howie-j/opensolder/mechanical/images/side_1.png

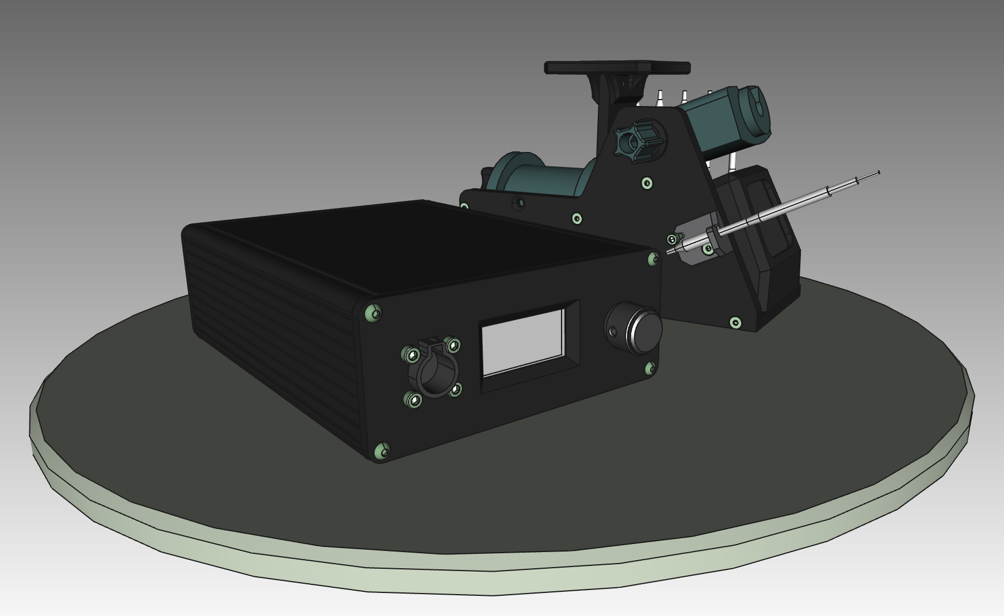
mechanical/images/side_1.png
