howie-j/opensolder/mechanical/images/top_3_ortho.png

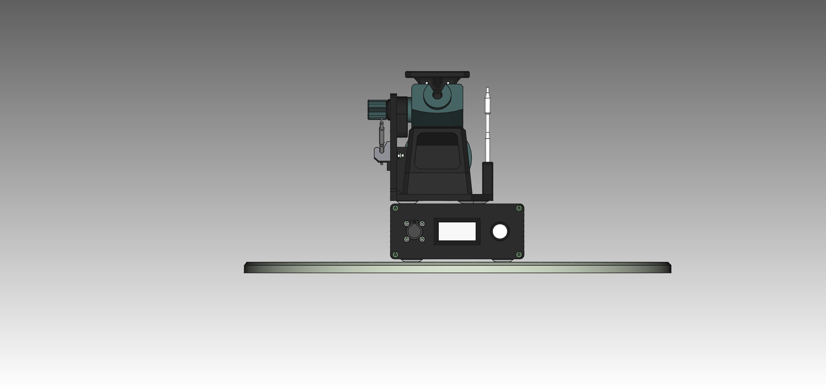
mechanical/images/top_3_ortho.png
