howie-j/opensolder/mechanical/step/stand_step_files/tool_holder_adapter.step

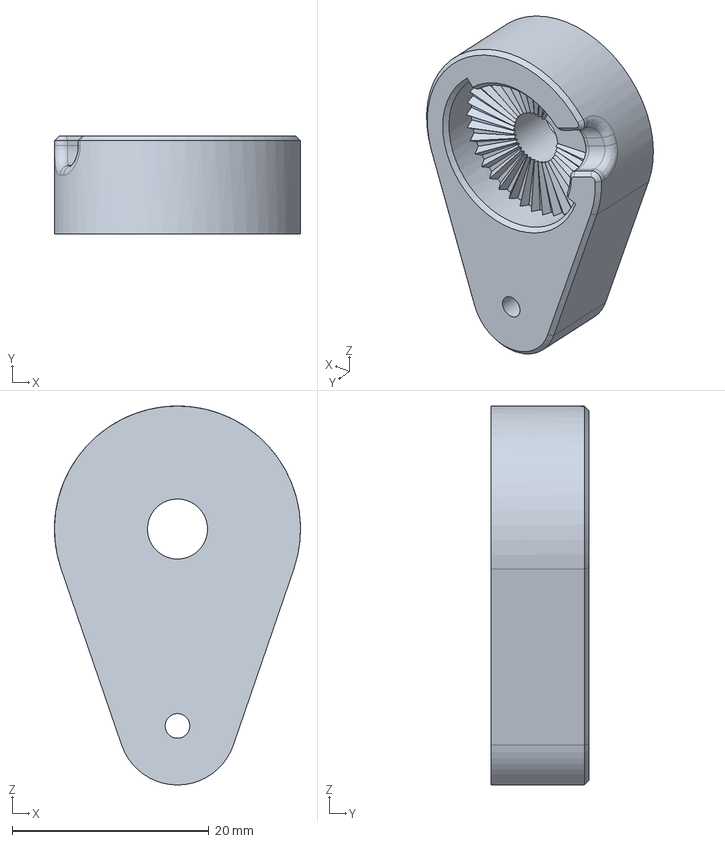
[picture p28: CAD file, 2023-04-08]
mechanical/step/stand_step_files/tool_holder_adapter.step
25.0 x 10.0 x 38.5 mm
