howie-j/opensolder/mechanical/freecad/Parts/Rotary Encoder Knob.FCStd

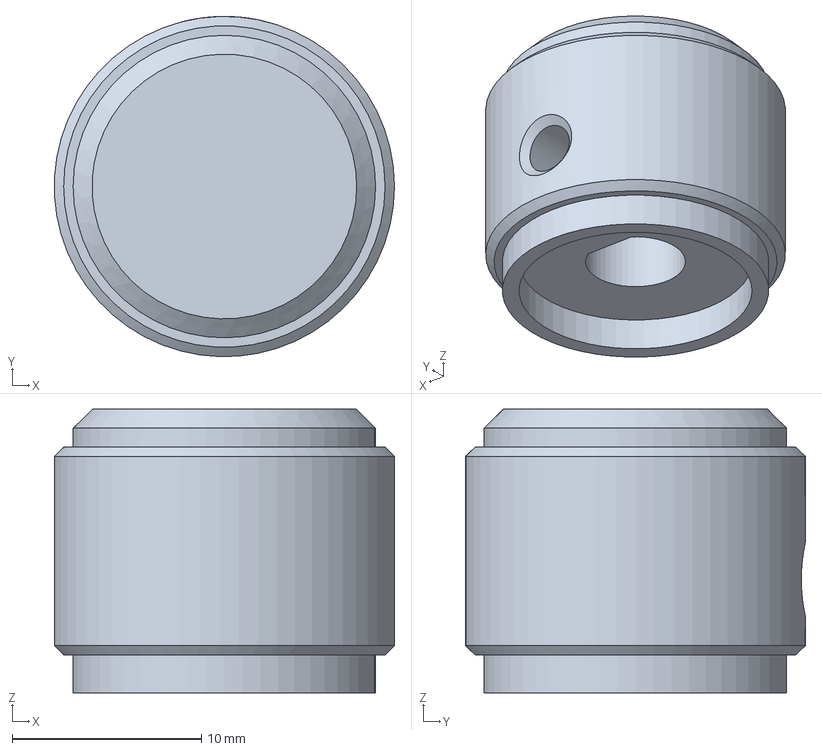
[picture p29: CAD file, 2023-04-08]
mechanical/freecad/Parts/Rotary Encoder Knob.FCStd
18.0 x 18.0 x 15.0 mm
