howie-j/opensolder/mechanical/step/stand_step_files/handle.step

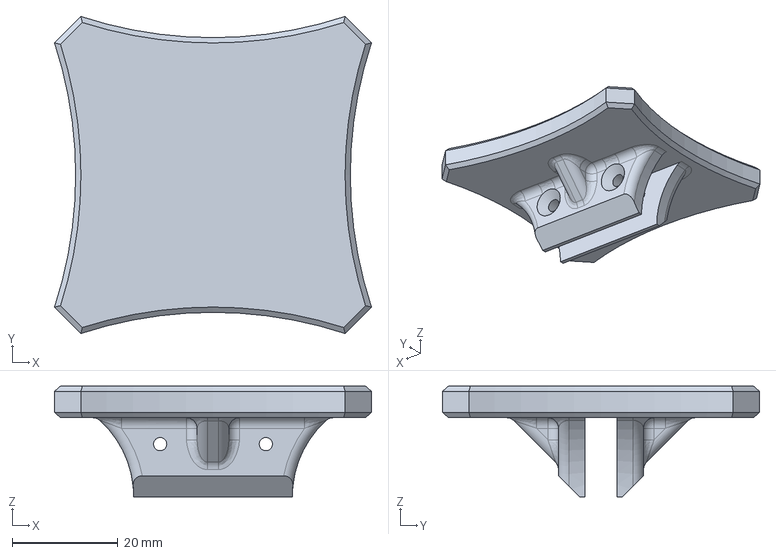
[picture p30: CAD file, 2023-04-08]
mechanical/step/stand_step_files/handle.step
60.0 x 60.0 x 21.0 mm
