howie-j/opensolder/mechanical/freecad/Parts/Tool Holder.FCStd

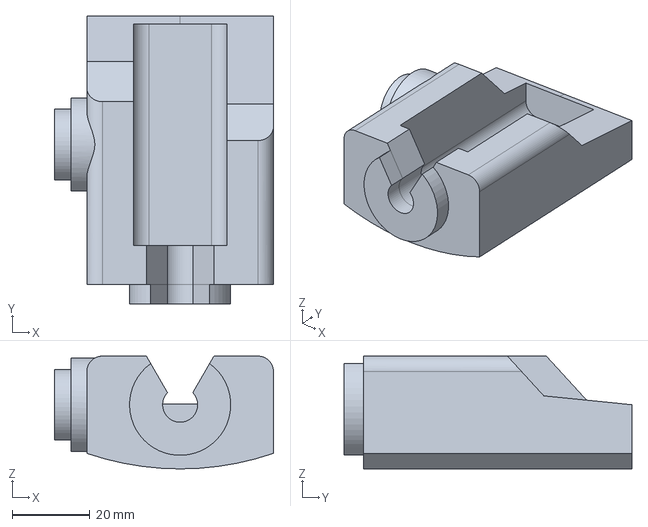
[picture p31: CAD file, 2023-04-08]
mechanical/freecad/Parts/Tool Holder.FCStd
56.3 x 74.0 x 29.0 mm
