howie-j/opensolder/mechanical/step/stand_step_files/tip_cleaner_right.step

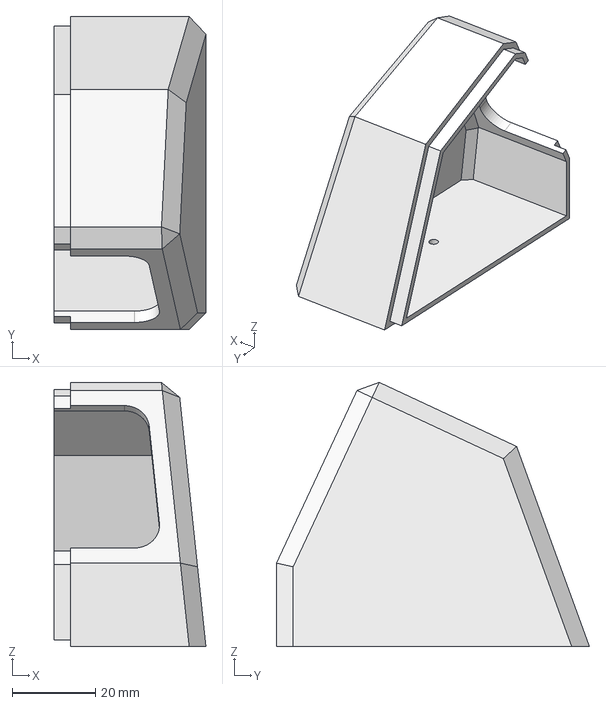
[picture p32: CAD file, 2023-04-08]
mechanical/step/stand_step_files/tip_cleaner_right.step
36.4 x 75.0 x 63.3 mm
