howie-j/opensolder/mechanical/freecad/Parts/Tip Cleaner.FCStd

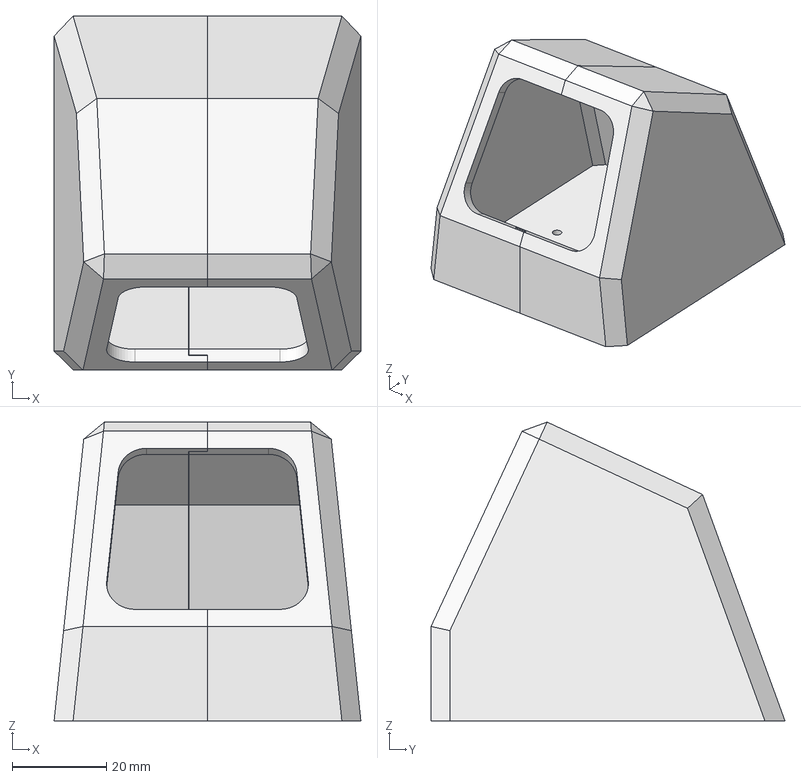
[picture p33: CAD file, 2023-04-08]
mechanical/freecad/Parts/Tip Cleaner.FCStd
65.0 x 75.0 x 63.3 mm
Tip_Cleaner
Left
Right
