howie-j/opensolder/mechanical/freecad/Parts/Transformer Spacer.FCStd

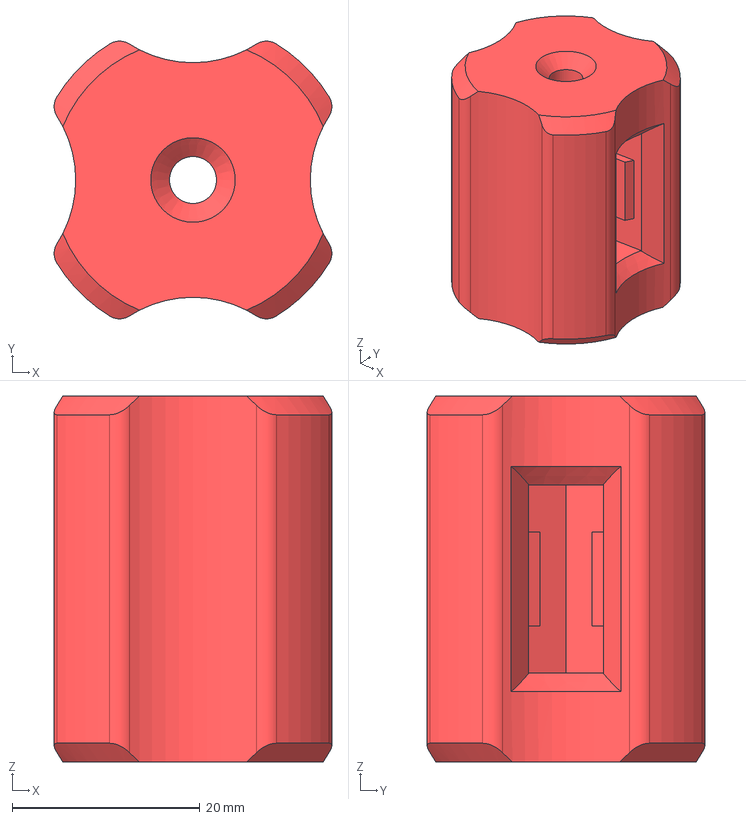
[picture p34: CAD file, 2023-04-08]
mechanical/freecad/Parts/Transformer Spacer.FCStd
29.6 x 29.6 x 39.0 mm
