howie-j/opensolder/mechanical/step/stand_step_files/tip_cleaner_left.step

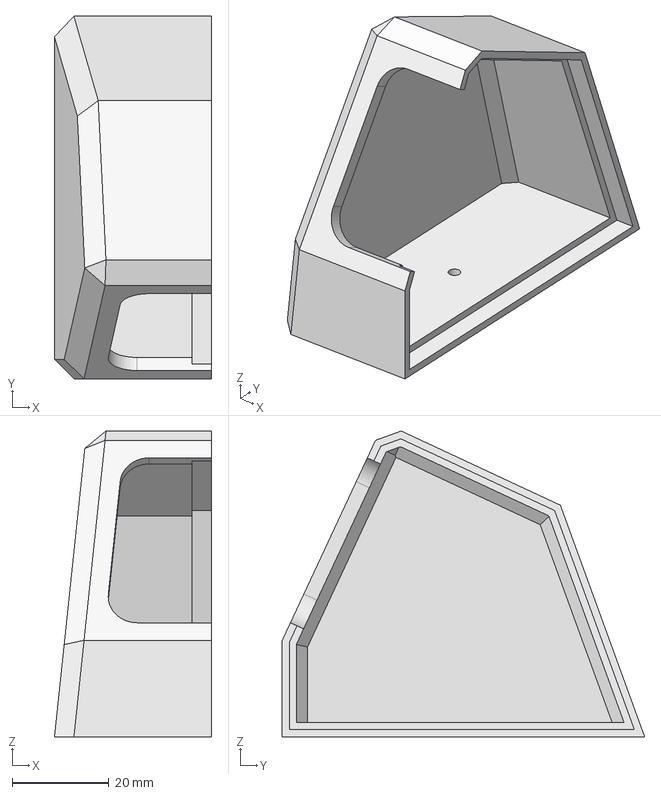
[picture p35: CAD file, 2023-04-08]
mechanical/step/stand_step_files/tip_cleaner_left.step
32.5 x 75.0 x 63.3 mm
