howie-j/opensolder/mechanical/freecad/Parts/PCB.FCStd

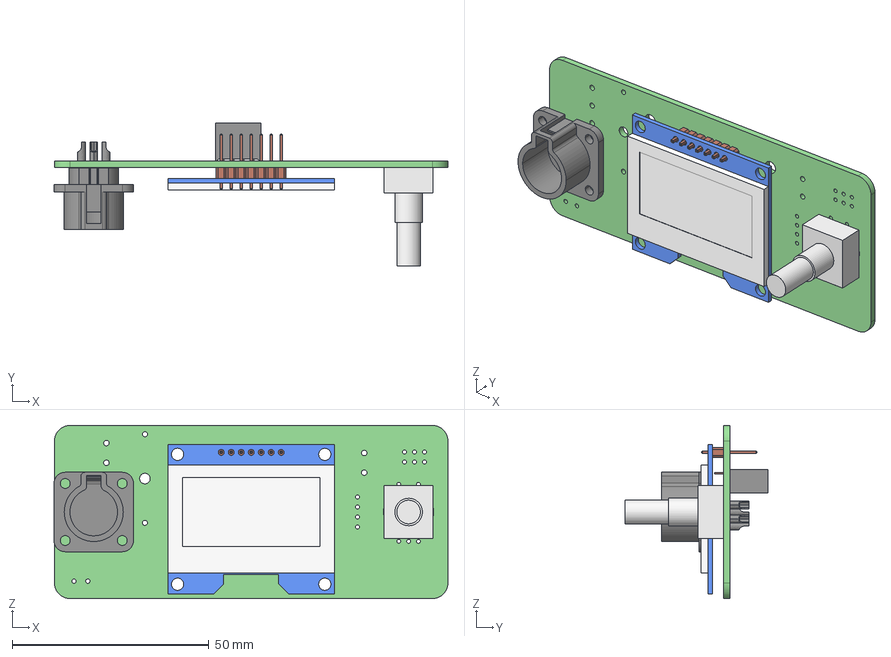
[picture p36: CAD file, 2023-04-08]
mechanical/freecad/Parts/PCB.FCStd
100.1 x 36.2 x 44.0 mm
openSolderV0.2 PCB
PEC11R
