howie-j/opensolder/mechanical/step/stand_step_files/mid_panel.step

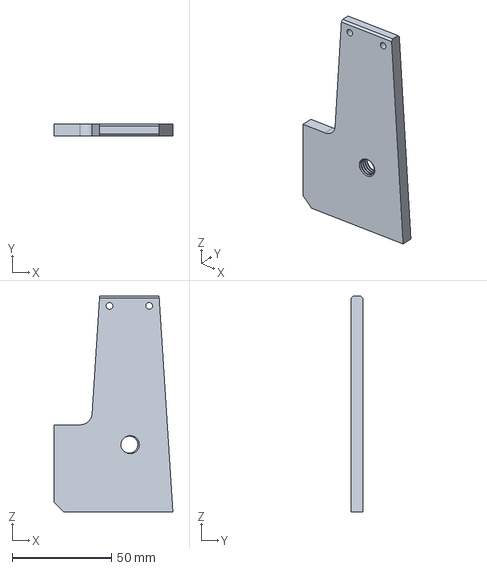
[picture p37: CAD file, 2023-04-08]
mechanical/step/stand_step_files/mid_panel.step
60.0 x 6.00 x 109.0 mm
