howie-j/opensolder/mechanical/step/stand_step_files/base_panel.step

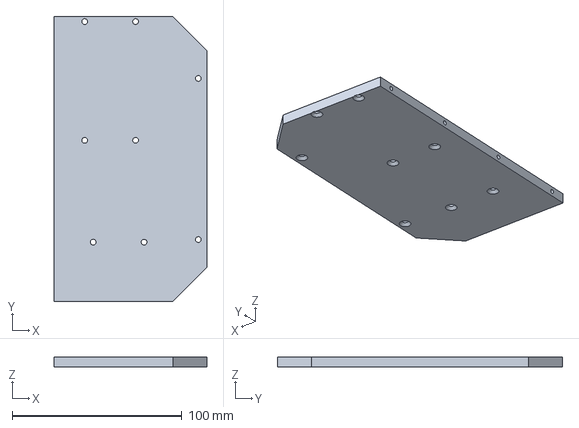
[picture p38: CAD file, 2023-04-08]
mechanical/step/stand_step_files/base_panel.step
90.0 x 168.0 x 6.00 mm
