howie-j/opensolder/mechanical/step/stand_step_files/rear_panel.step

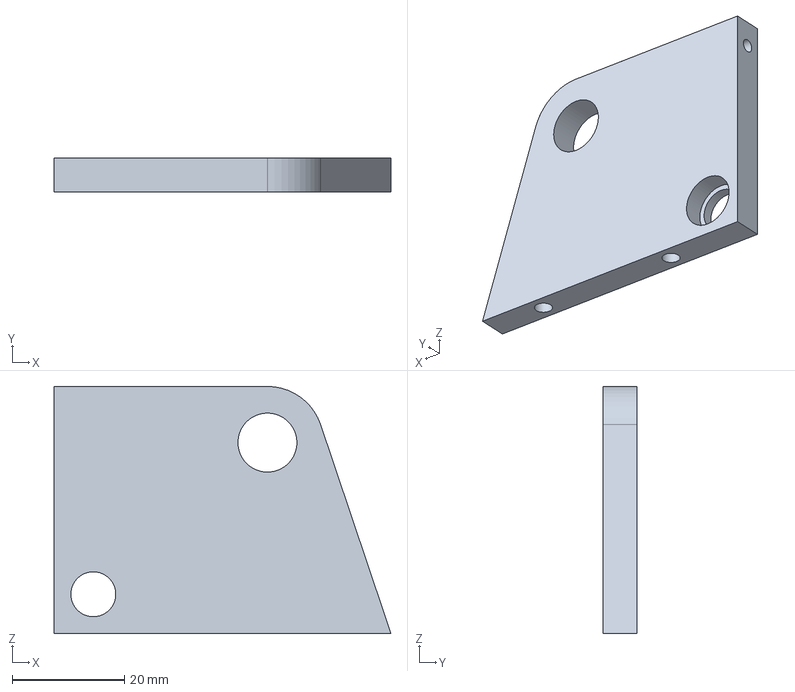
[picture p39: CAD file, 2023-04-08]
mechanical/step/stand_step_files/rear_panel.step
60.0 x 6.00 x 44.0 mm
