howie-j/opensolder/mechanical/freecad/Parts/Rubber Pad.FCStd

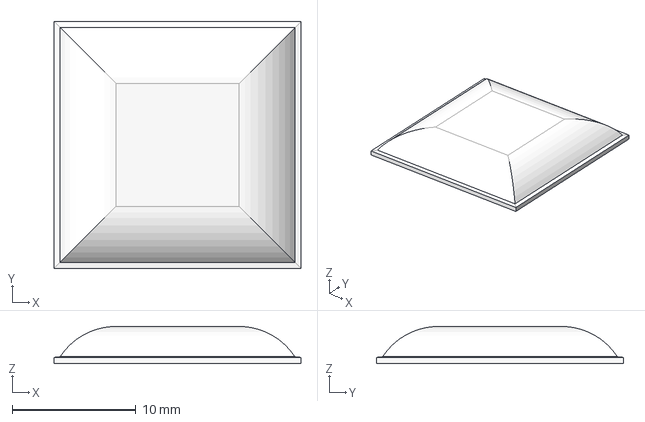
[picture p40: CAD file, 2023-04-08]
mechanical/freecad/Parts/Rubber Pad.FCStd
20.0 x 20.0 x 3.00 mm
