howie-j/opensolder/mechanical/freecad/Parts/Spool Dummy.FCStd

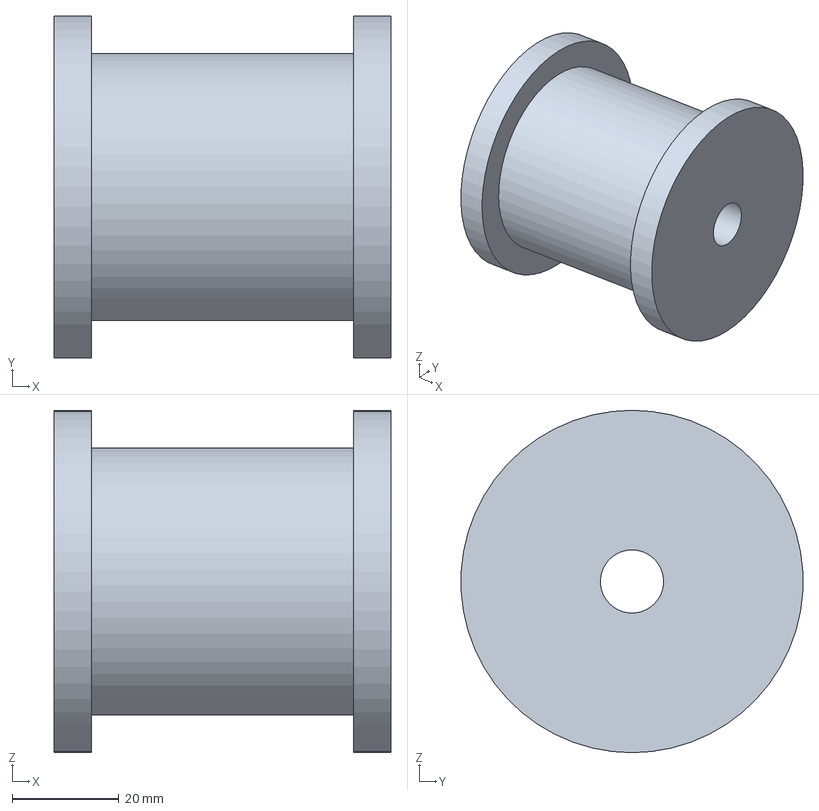
[picture p41: CAD file, 2023-04-08]
mechanical/freecad/Parts/Spool Dummy.FCStd
63.0 x 63.9 x 64.0 mm
