howie-j/opensolder/mechanical/step/stand_step_files/tip_cleaner_single.step

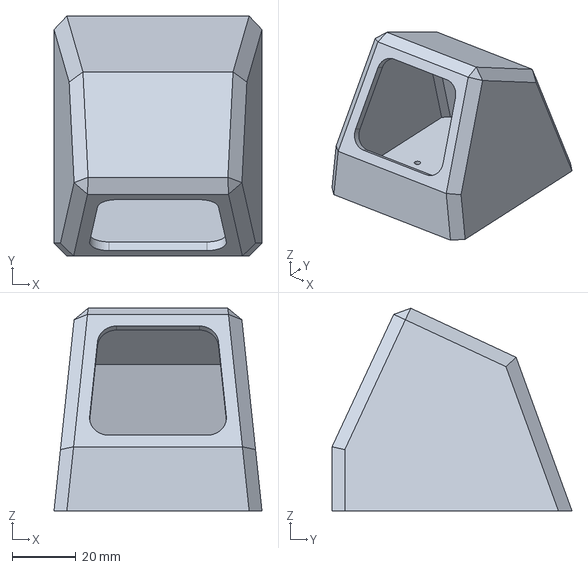
[picture p42: CAD file, 2023-04-08]
mechanical/step/stand_step_files/tip_cleaner_single.step
65.0 x 75.0 x 63.3 mm
