howie-j/opensolder/mechanical/freecad/Parts/Enclosure 1455Q1602BK.FCStd

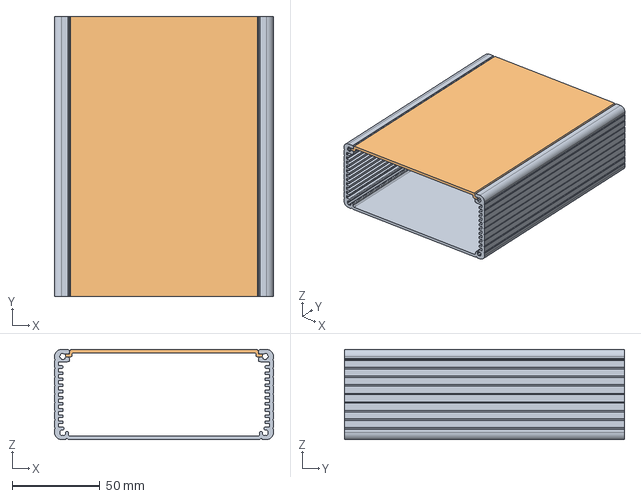
[picture p43: CAD file, 2023-04-08]
mechanical/freecad/Parts/Enclosure 1455Q1602BK.FCStd
125.0 x 160.0 x 51.5 mm
Enclosure_1455Q1602BK_Extrusion
Enclosure_1455Q1602BK_Cap
