howie-j/opensolder/mechanical/freecad/Parts/Connector IEC-C14 703W-0004.FCStd

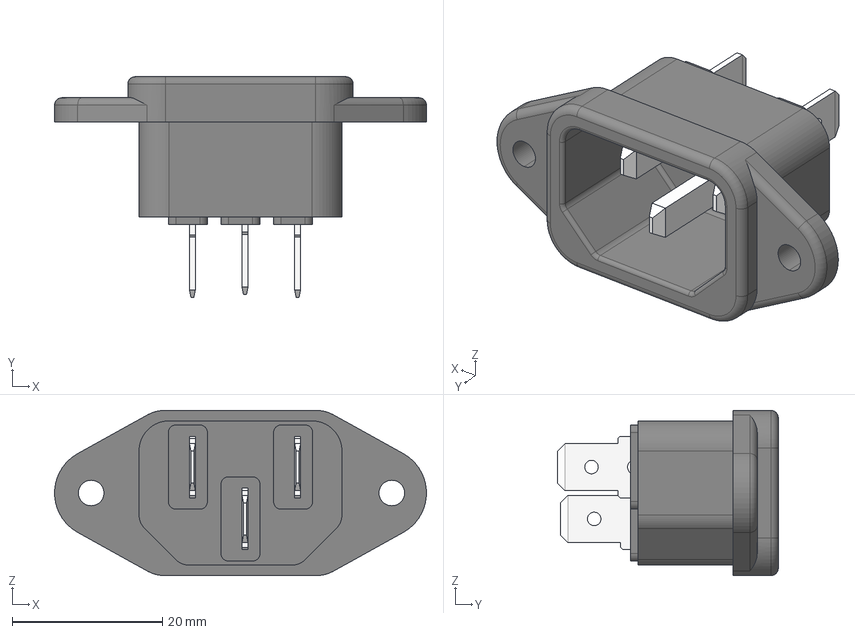
[picture p44: CAD file, 2023-04-08]
mechanical/freecad/Parts/Connector IEC-C14 703W-0004.FCStd
49.5 x 29.4 x 22.0 mm
SS7BVDERB
SS7B-001-63
SS7B-002-63
SS7B-002-064
