howie-j/opensolder/mechanical/freecad/Parts/Connector Minijack MJ-064H.FCStd

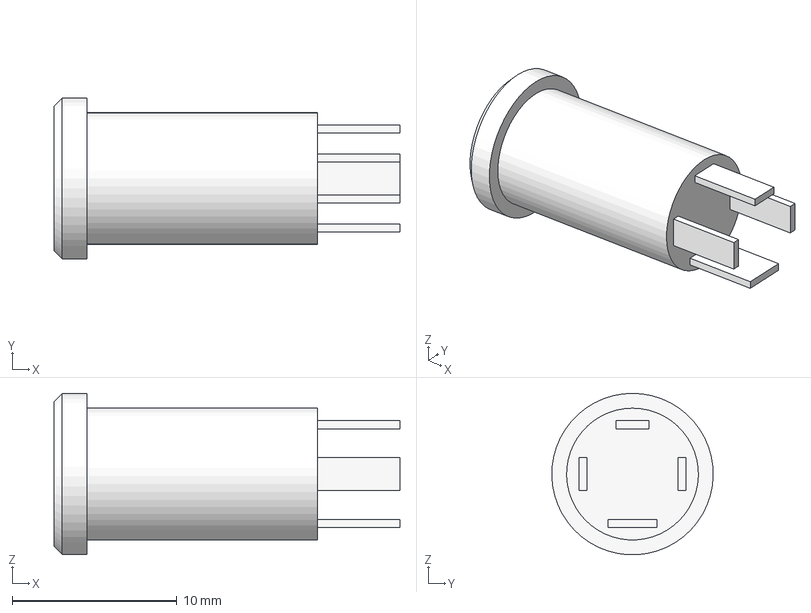
[picture p45: CAD file, 2023-04-08]
mechanical/freecad/Parts/Connector Minijack MJ-064H.FCStd
21.0 x 9.80 x 9.79 mm
