howie-j/opensolder/mechanical/freecad/Parts/Transformer.FCStd

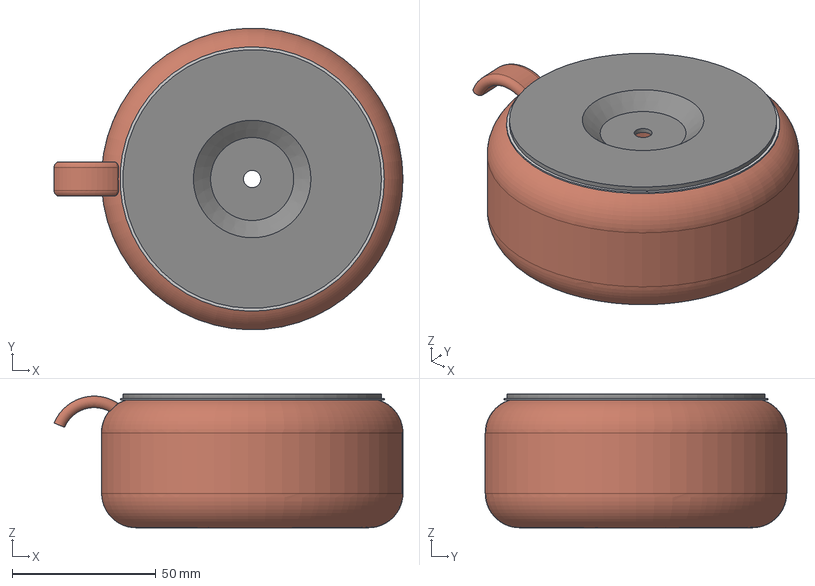
[picture p46: CAD file, 2023-04-08]
mechanical/freecad/Parts/Transformer.FCStd
121.5 x 105.0 x 46.5 mm
Transformer
Foam
Transformer_Washer
