howie-j/opensolder/mechanical/freecad/Parts/Tip Dummy.FCStd

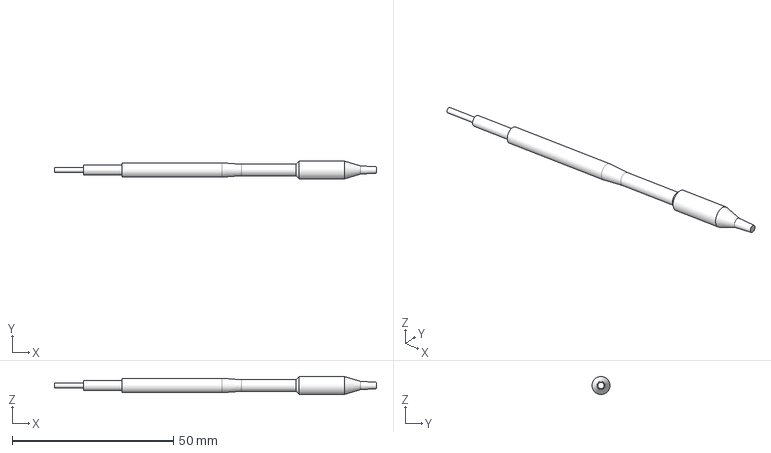
[picture p47: CAD file, 2023-04-08]
mechanical/freecad/Parts/Tip Dummy.FCStd
100.0 x 5.60 x 5.59 mm
